Codethetical/sucralose/docs/img/chalk-layout-left.png

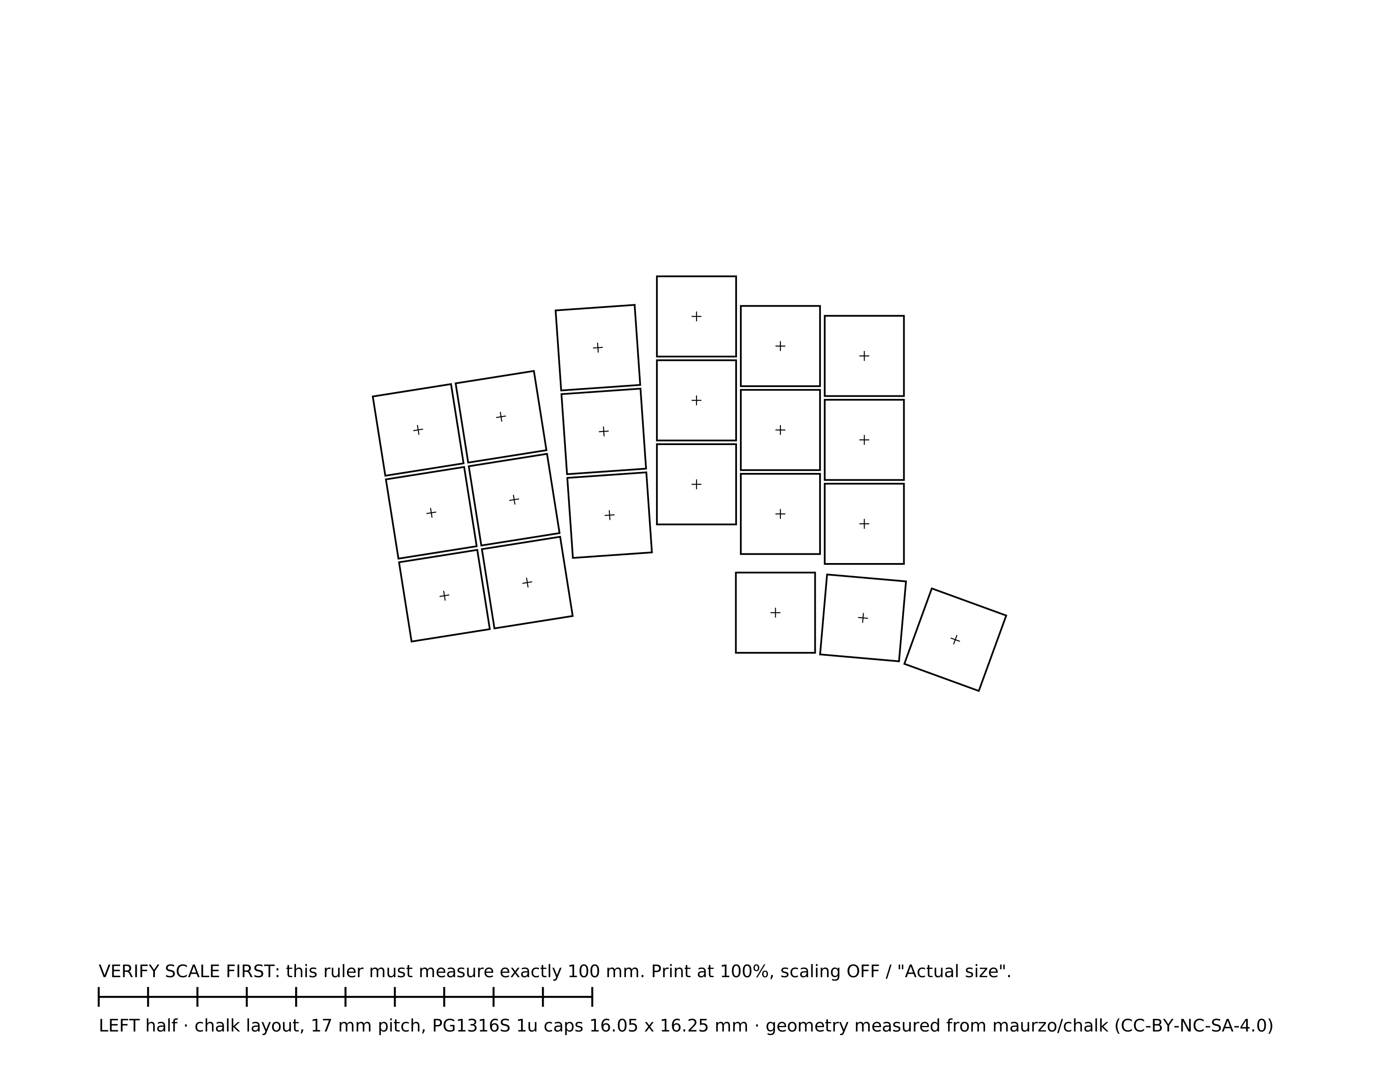
docs/img/chalk-layout-left.png
