Codethetical/sucralose/docs/img/chevron-jumper-JP2.png

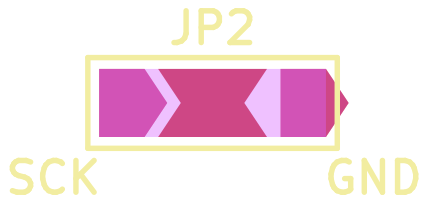
docs/img/chevron-jumper-JP2.png
