Codethetical/sucralose/docs/img/CPG1316S01D02_th_reversible_sucralose.png

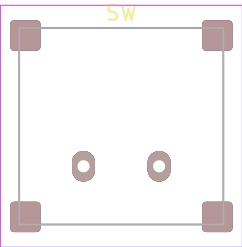
docs/img/CPG1316S01D02_th_reversible_sucralose.png
