Codethetical/sucralose/docs/img/pcb-outline-render.png

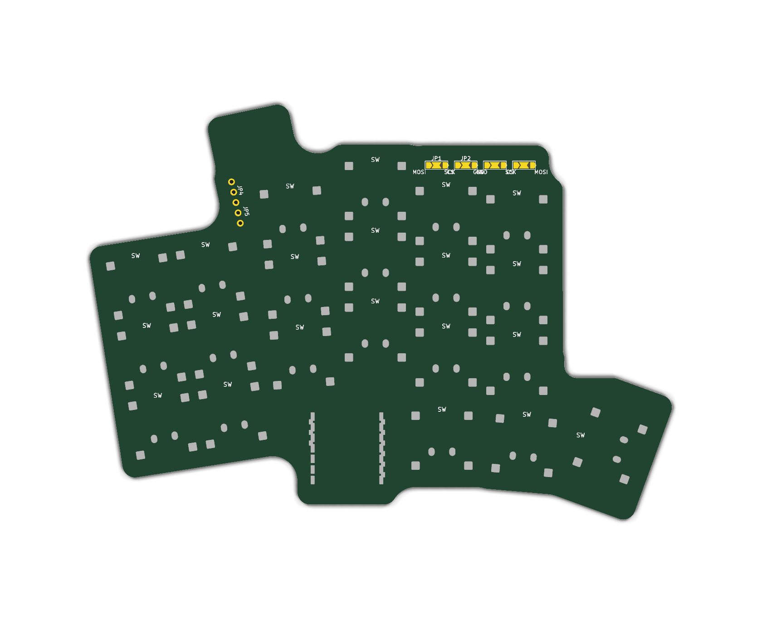
docs/img/pcb-outline-render.png
