Codethetical/sucralose/docs/img/pcb-placed-render.png

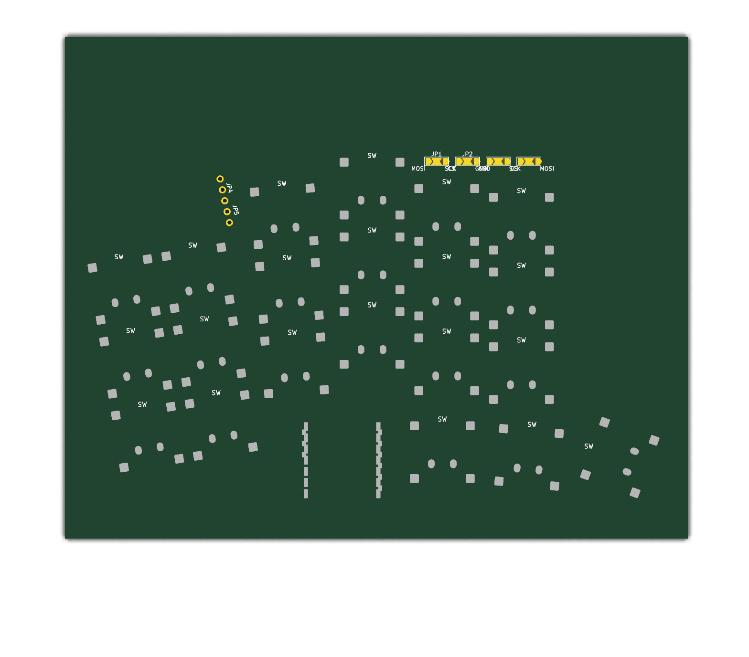
docs/img/pcb-placed-render.png
