Codethetical/sucralose/docs/img/pcb-placement-render.png

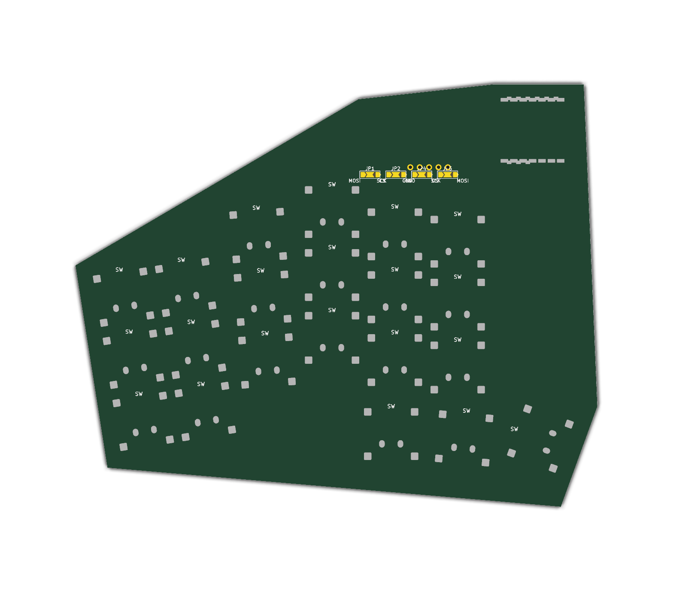
docs/img/pcb-placement-render.png
