Codethetical/sucralose/docs/img/SW_PG1316M_th_reversible_sucralose.png

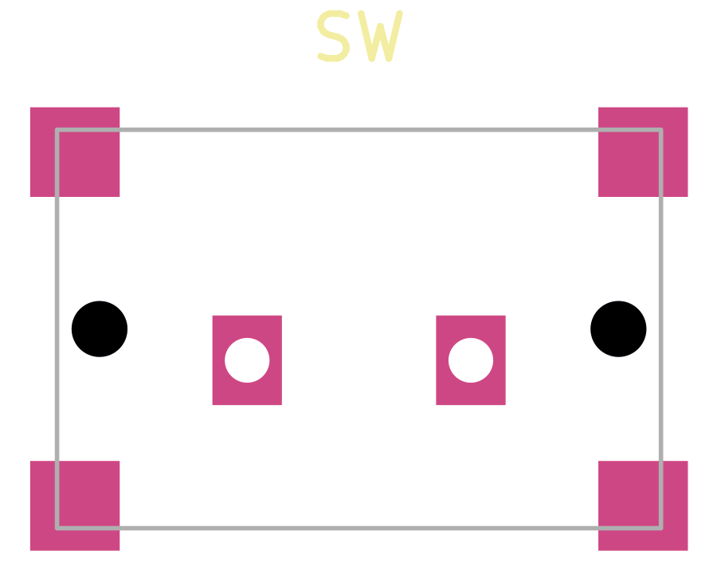
docs/img/SW_PG1316M_th_reversible_sucralose.png
