Codethetical/sucralose/docs/img/xiao-reversible-land.png

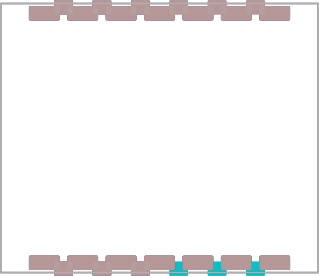
docs/img/xiao-reversible-land.png
