Codethetical/sucralose/pics/rev1-front-profile.jpg

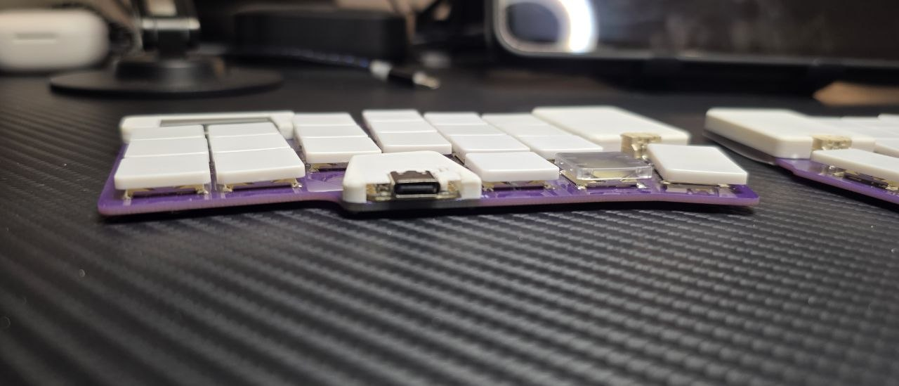
pics/rev1-front-profile.jpg
