Codethetical/sucralose/pics/rev1-stacked-side-profile.jpg

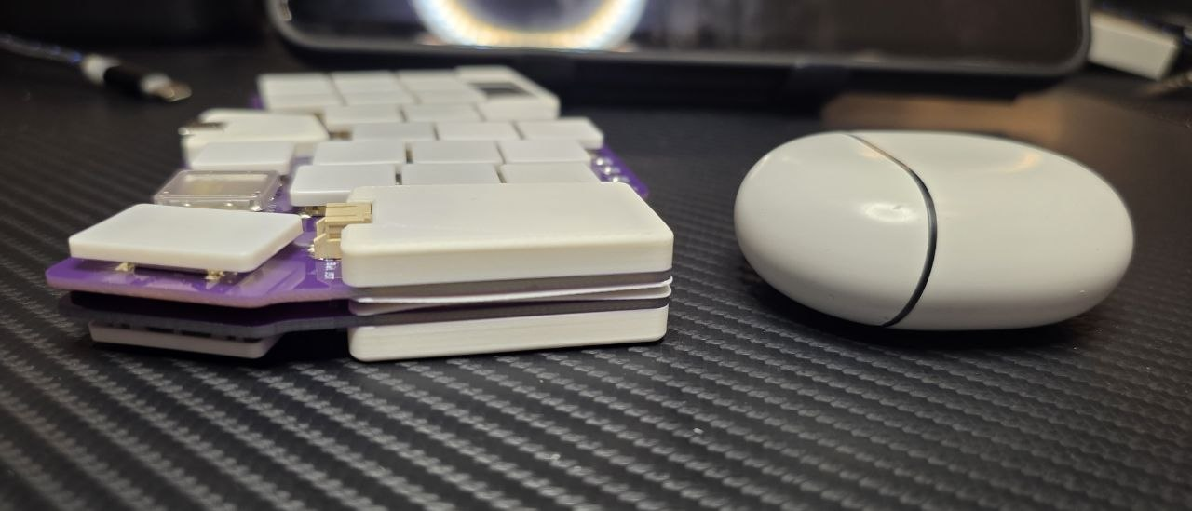
pics/rev1-stacked-side-profile.jpg
