Codethetical/sucralose/pics/rev1-top-display-left.jpg

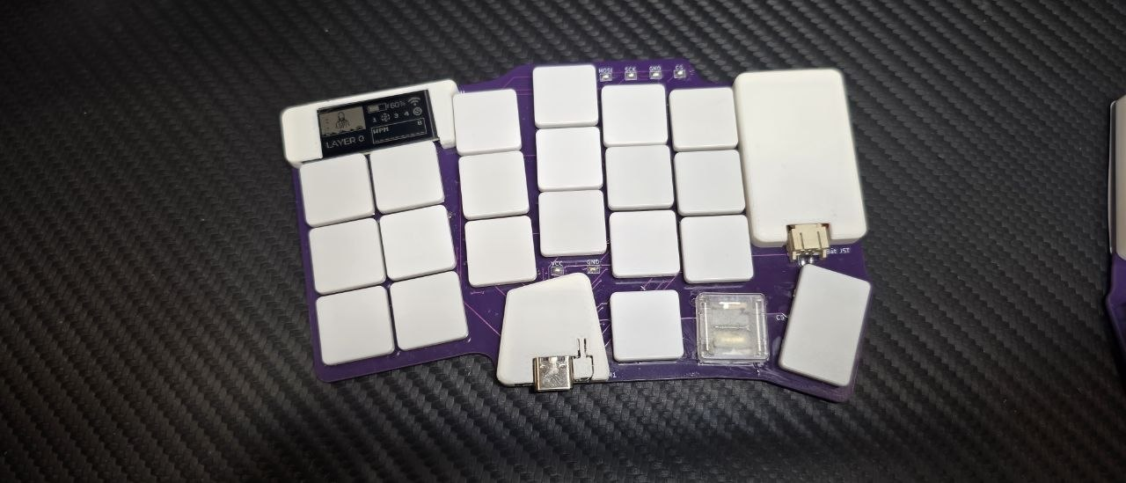
pics/rev1-top-display-left.jpg
