Codethetical/sucralose/pics/rev1-top-display-right.jpg

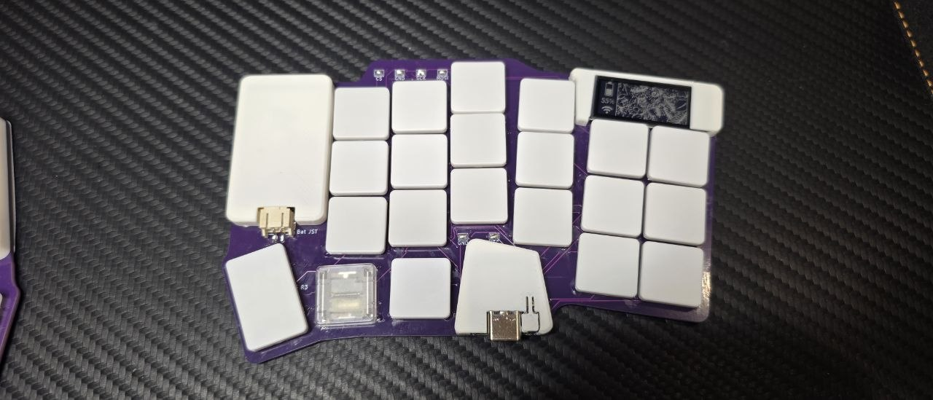
pics/rev1-top-display-right.jpg
