Codethetical/sucralose/pics/sucralose-battery-edge.png

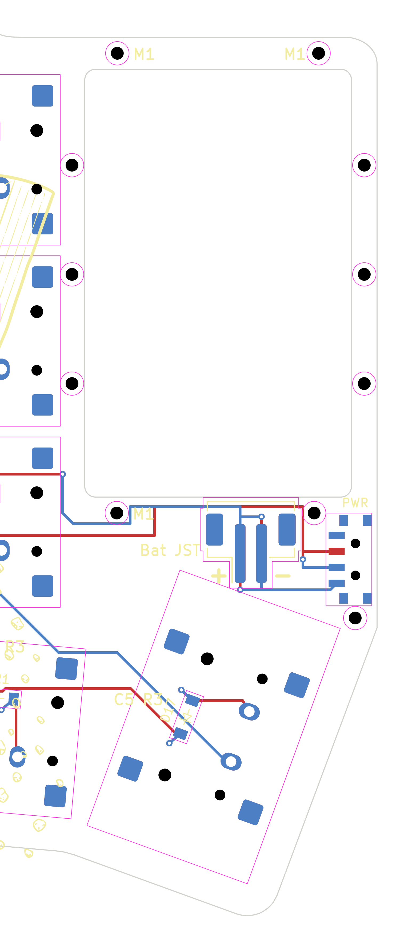
pics/sucralose-battery-edge.png
