Codethetical/sucralose/pics/sucralose-display-m1.png

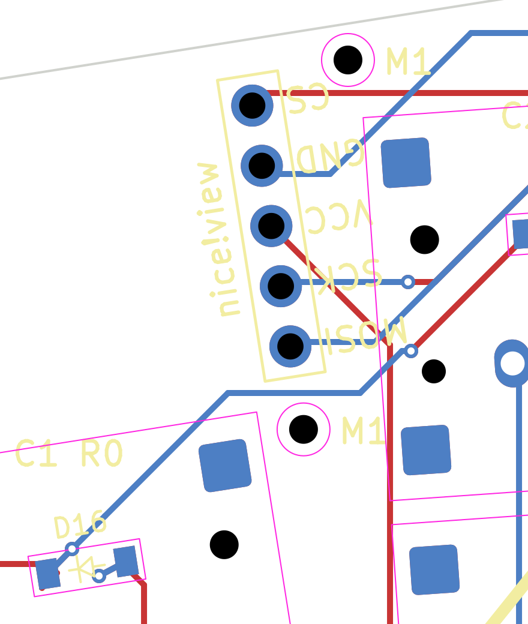
pics/sucralose-display-m1.png
