Codethetical/sucralose/pics/sucralose-pinky-col7-mock.png

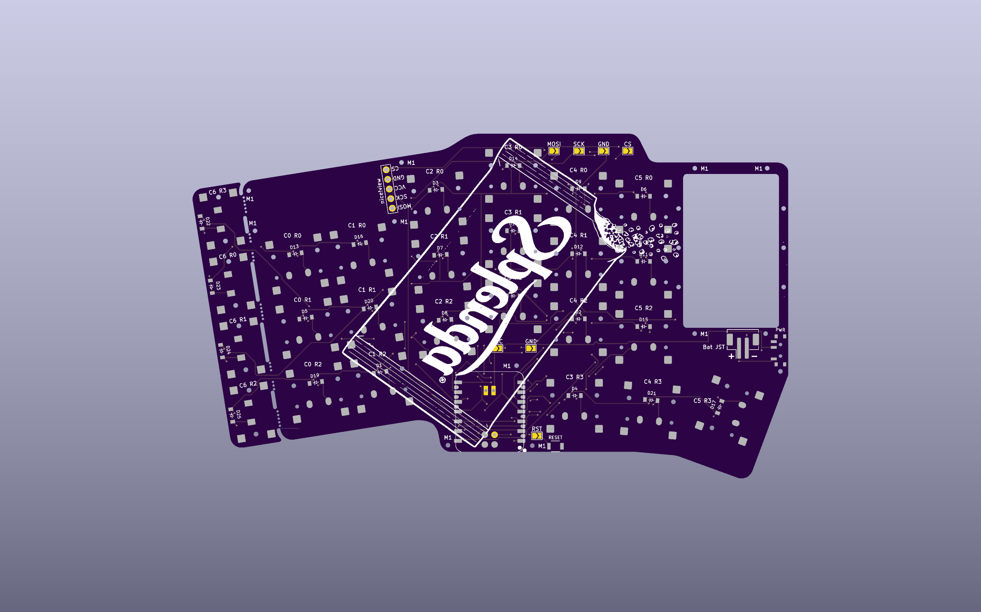
pics/sucralose-pinky-col7-mock.png
