Codethetical/sucralose/docs/img/component-mockup.jpg

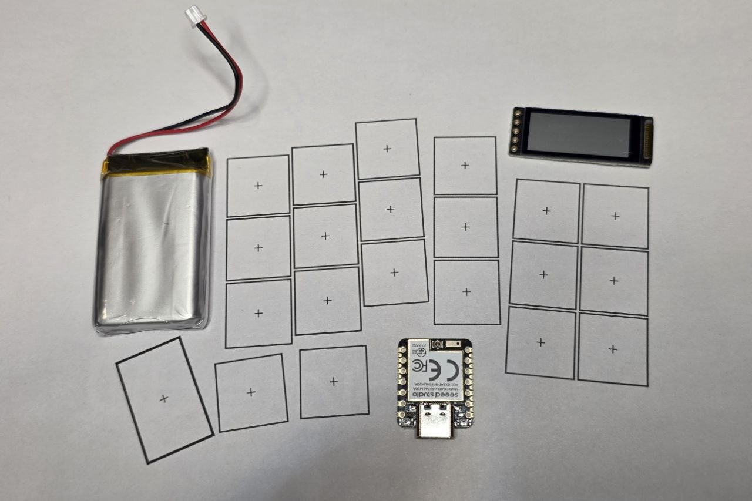
docs/img/component-mockup.jpg
